lizardsystems/yawl-controller/images/flash.jpg

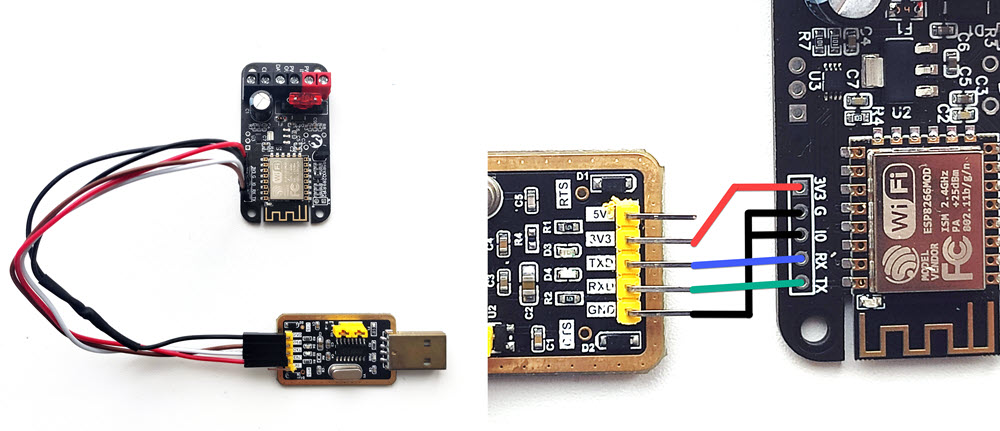
images/flash.jpg
