lizardsystems/yawl-controller/images/yawl-controller-manual-soldered.jpg

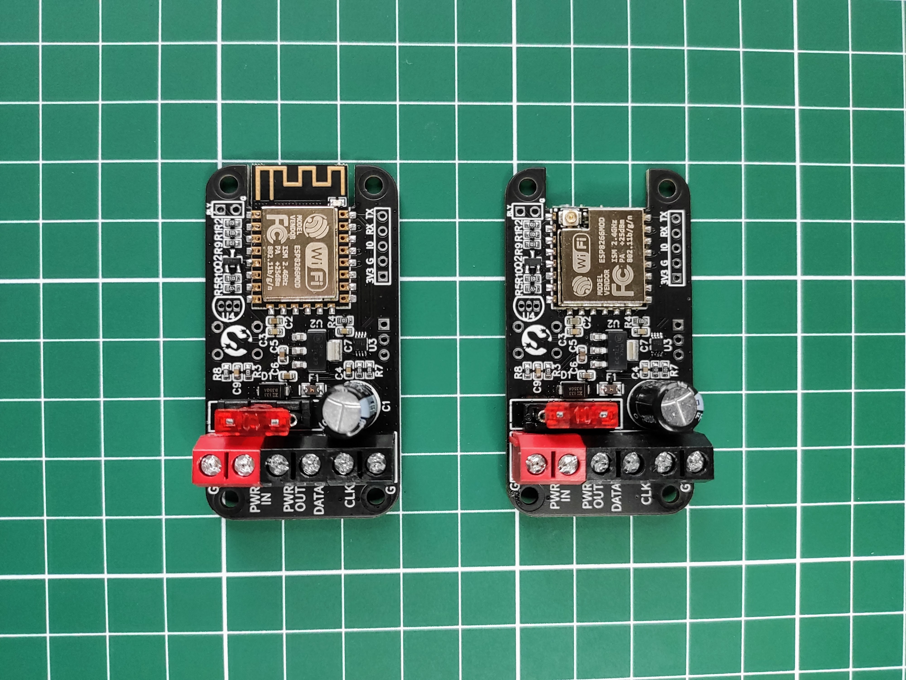
images/yawl-controller-manual-soldered.jpg
