lizardsystems/yawl-controller/images/yawl-controller-manual-soldering.jpg

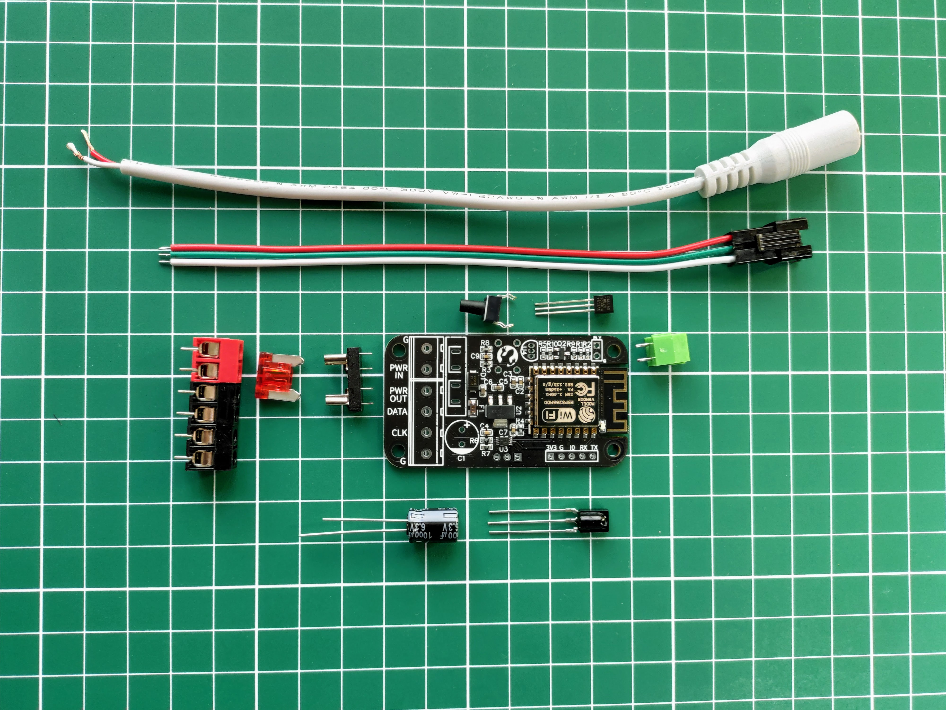
images/yawl-controller-manual-soldering.jpg
